bluepylons/USB-C-3-way-splitter/Graphics/PCB.JPG

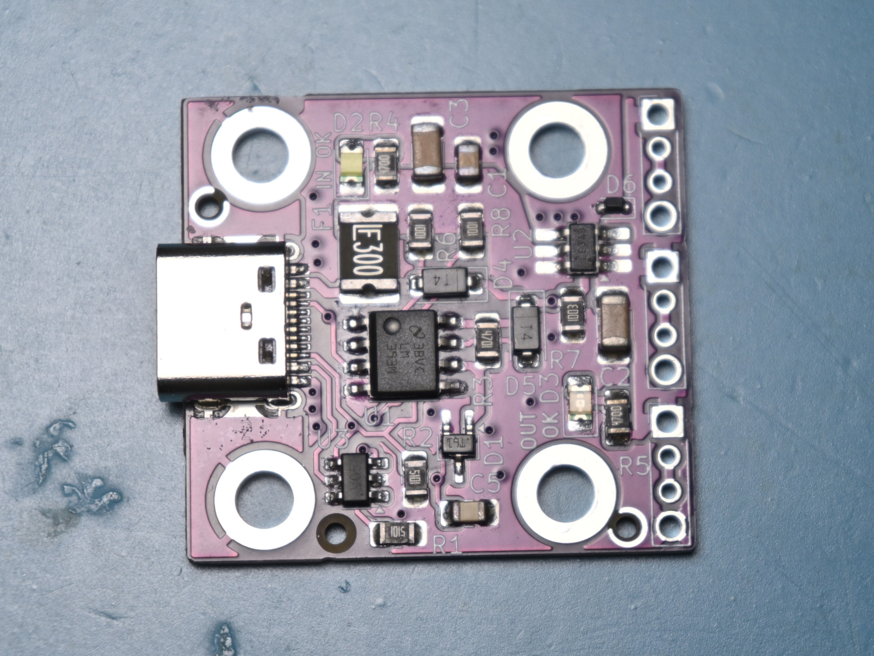
Graphics/PCB.JPG
