bluepylons/USB-C-3-way-splitter/Graphics/thermal-pad-location.PNG

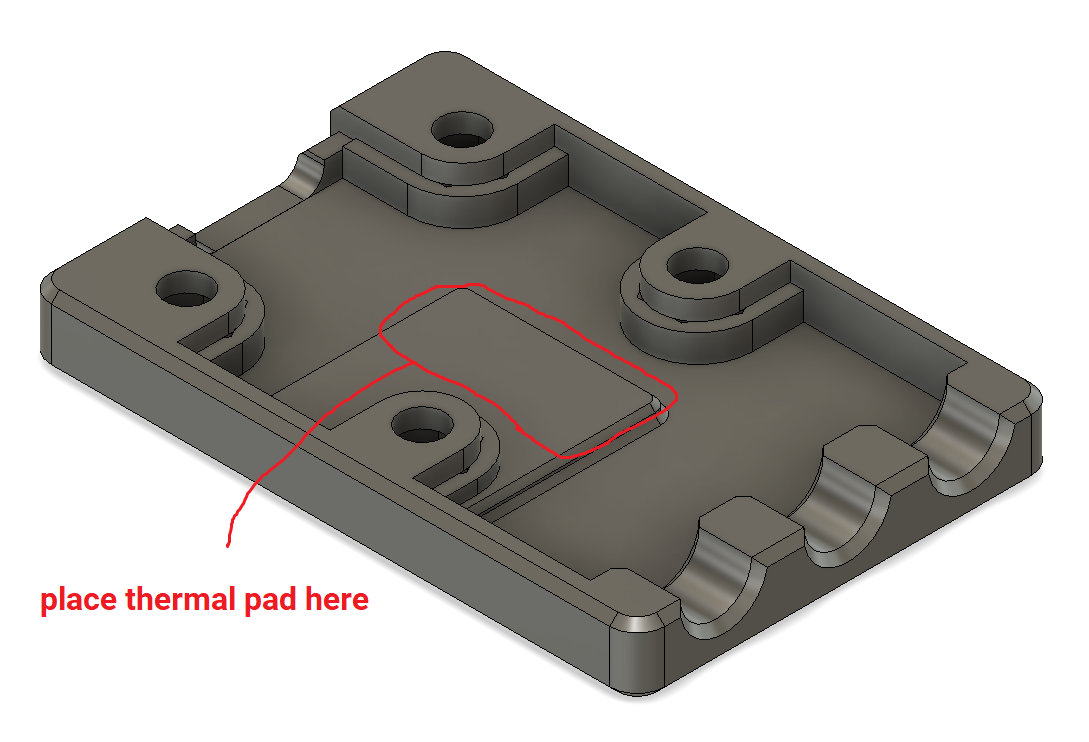
Graphics/thermal-pad-location.PNG
